mattguo5/RFID-VWC/Code/Adafruit_Logging/Logger_Box.ino

///////////////////////////////////////////////////////////////////////////////

// This is an example to use with the Loom Multiplexer to enable you to 
// dynamically connect any Loom-supported I2C sensors

// The code is essentially the same a 'Basic', the only real different is the
// enabling of the Multiplexer in the configuration.

///////////////////////////////////////////////////////////////////////////////

#include <Loom.h>

// Include configuration
const char* json_config = 
#include "config.h"
;

// Set enabled modules
LoomFactory<
	Enable::Internet::Disabled,
	Enable::Sensors::Enabled,
	Enable::Radios::Disabled,
	Enable::Actuators::Disabled,
	Enable::Max::Disabled
> ModuleFactory{};

LoomManager Loom{ &ModuleFactory };

int other = 0;

void setup() 
{ 
	Loom.begin_serial(true);
	Loom.parse_config(json_config);
	Loom.print_config();

	LPrintln("\n ** Setup Complete ** ");
}

void loop() 
{
	Loom.measure();
	Loom.package();
	Loom.display_data();
  Loom.add_data("EPC", "EPC", other);
  Loom.SDCARD().log();
  other++;
	Loom.pause();
}
